MaesterK/atari-hypercard/pictures/flowmenu.png

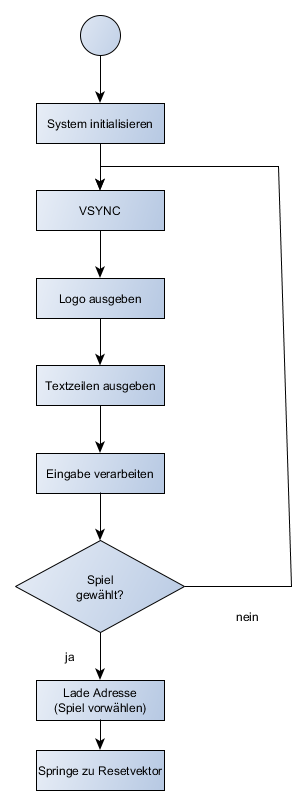
pictures/flowmenu.png
