MaesterK/atari-hypercard/pictures/galstate.png

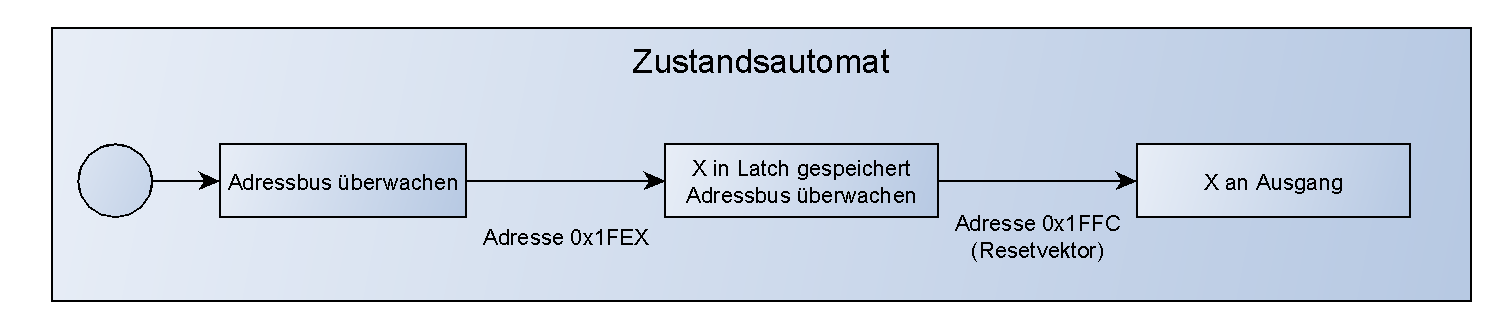
pictures/galstate.png
