MaesterK/atari-hypercard/pictures/menueexplained2.png

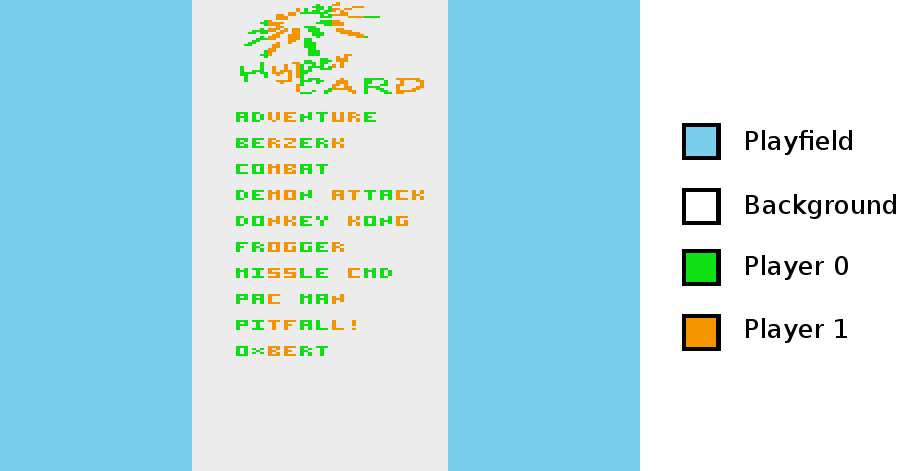
pictures/menueexplained2.png
