MaesterK/atari-hypercard/pictures/menueexplained_work.png

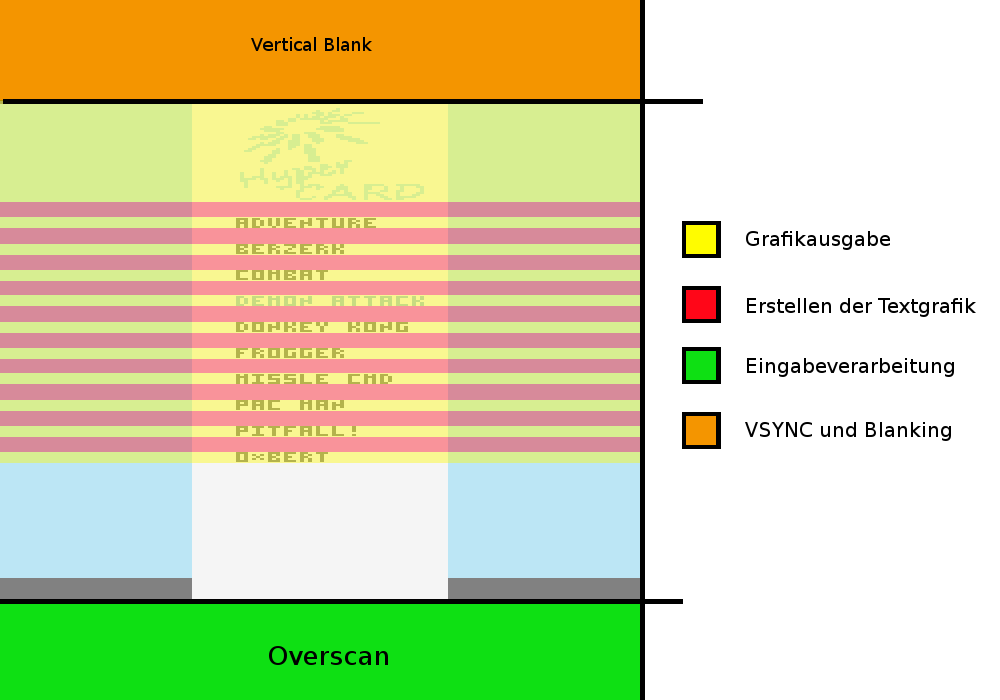
pictures/menueexplained_work.png
