MaesterK/atari-hypercard/pictures/supercard.png

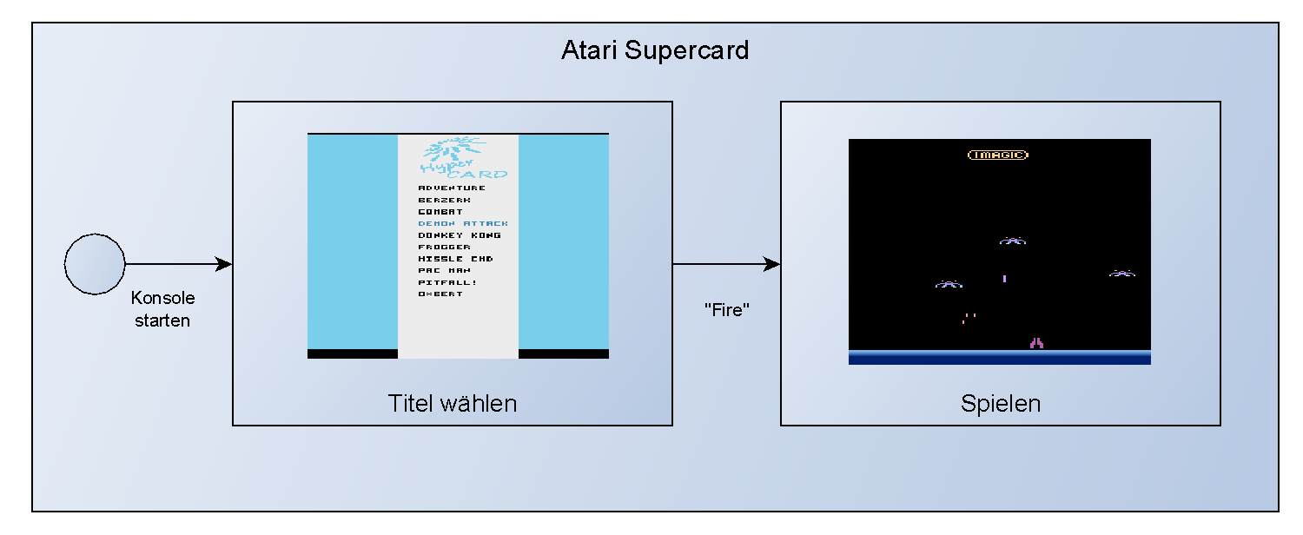
pictures/supercard.png
