MaesterK/atari-hypercard/pictures/wappen.PNG

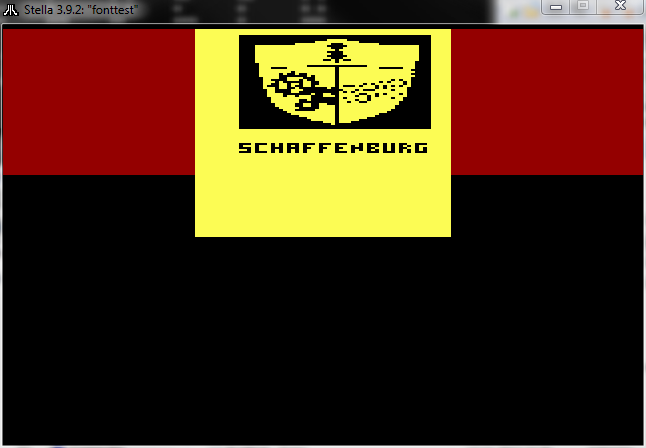
pictures/wappen.PNG
