MaesterK/atari-hypercard/pictures/debugger.PNG

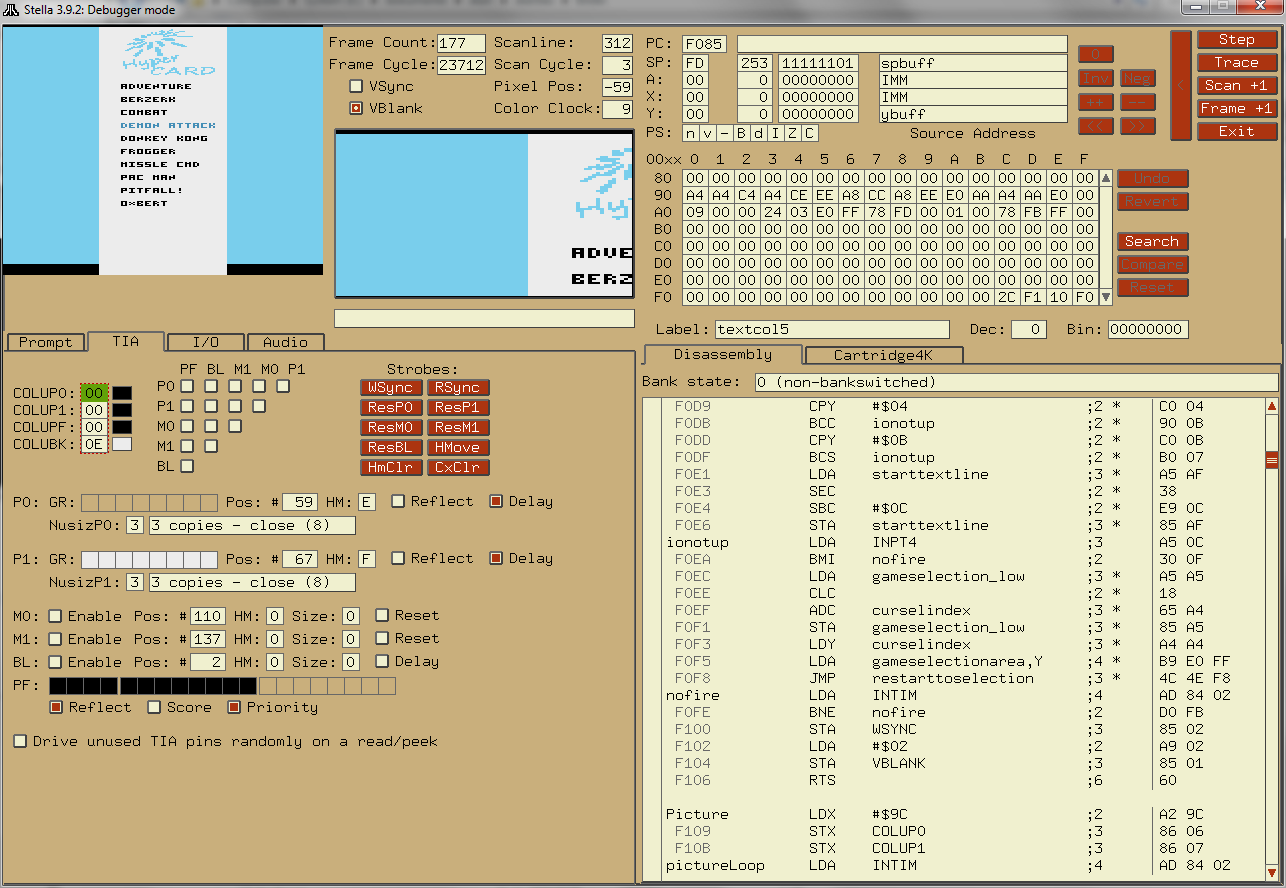
pictures/debugger.PNG
