MaesterK/atari-hypercard/tools/main2.cpp

#include <iostream>

/* run this program using the console pauser or add your own getch, system("pause") or input loop */


unsigned char pic[]={0x00,0x00,0x00,0x00,0x00,0x00
,0x00,0x00,0x00,0x40,0x00,0x00
,0x00,0x00,0x08,0xc0,0x00,0x00
,0x00,0x00,0x1d,0x07,0x00,0x00
,0x00,0x01,0x4d,0xd8,0x00,0x00
,0x00,0x01,0x5b,0xa0,0x00,0x00
,0x00,0x06,0xfe,0x30,0x00,0x00
,0x00,0x36,0x05,0xf0,0x00,0x00
,0x00,0x38,0x07,0x0f,0xf0,0x00
,0x00,0x38,0x00,0x00,0x00,0x00
,0x01,0x80,0x07,0xc0,0x00,0x00
,0x03,0xf0,0x0f,0xe0,0x00,0x00
,0x01,0xe0,0x03,0xe0,0x00,0x00
,0x00,0x30,0x70,0x00,0x00,0x00
,0x02,0xeb,0x38,0x60,0x00,0x00
,0x0f,0xdb,0x38,0x78,0x00,0x00
,0x1b,0x33,0x1c,0x3e,0x00,0x00
,0x00,0x67,0x1c,0x0f,0x00,0x00
,0x02,0xe7,0x08,0x03,0x80,0x00
,0x07,0xc7,0x60,0x00,0x00,0x00
,0x0c,0x06,0x60,0x00,0x00,0x00
,0x18,0x24,0x70,0x00,0x00,0x00
,0x30,0x60,0x70,0x00,0x00,0x00
,0x00,0x60,0x70,0x00,0x00,0x00
,0x00,0xc0,0x30,0x00,0x00,0x00
,0x01,0xc0,0x38,0x00,0x00,0x00
,0x01,0x80,0x38,0x00,0x00,0x00
,0x03,0x80,0x38,0x18,0x00,0x00
,0x01,0x00,0x00,0x50,0x00,0x00
,0x00,0x00,0x06,0x70,0x00,0x00
,0x00,0x00,0x67,0x70,0x00,0x00
,0x02,0x03,0x76,0x20,0x00,0x00
,0x02,0x09,0x94,0xa0,0x00,0x00
,0x42,0x49,0xbd,0xa0,0x00,0x00
,0x42,0x49,0xa7,0x00,0x00,0x00
,0x4e,0x5d,0xe0,0x00,0x00,0x00
,0x7b,0x75,0xc0,0x00,0x00,0x00
,0x61,0x25,0x80,0x00,0x00,0x00
,0x21,0x05,0x80,0x00,0x00,0x00
,0x20,0x04,0xb8,0x20,0xf8,0xfc
,0x20,0x3c,0xec,0x70,0xc4,0x46
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

};

//wappen
/*
{0xff,0xff,0xff,0xff,0xff,0xff
,0xff,0xff,0xff,0xff,0xff,0xff
,0xff,0xff,0xff,0xff,0xff,0xff
,0xff,0xff,0xfc,0x1f,0xff,0xff
,0xff,0xff,0xe0,0x03,0xff,0xff
,0xff,0xfc,0x01,0xc0,0x1f,0xff
,0xf0,0x00,0x03,0xe0,0x00,0x07
,0xf0,0x00,0x01,0xc0,0x00,0x07
,0xf0,0x00,0x00,0x80,0x00,0x07
,0xf0,0x00,0x03,0xc0,0x00,0x07
,0xf0,0x00,0x01,0xc0,0x00,0x07
,0xf0,0x00,0x03,0xe0,0x00,0x07
,0xf0,0x00,0x01,0xc0,0x00,0x07
,0xf0,0x00,0x06,0xb0,0x00,0x07
,0xf0,0x00,0x00,0x80,0x00,0x0f
,0xf8,0x00,0x00,0x00,0x00,0x0f
,0xf8,0x00,0x7f,0xff,0x00,0x0f
,0xf8,0xf0,0x00,0x80,0x1f,0x8f
,0xf8,0x00,0x00,0x80,0x00,0x1f
,0xf8,0x04,0x00,0x80,0x00,0x0f
,0xf8,0x2d,0x80,0x80,0x00,0x1f
,0xf8,0x3f,0xa0,0x80,0x00,0x0f
,0xfc,0x30,0xe0,0x80,0x00,0x1f
,0xfc,0xf1,0x60,0x80,0x02,0x9f
,0xfc,0x5f,0x30,0x80,0x14,0x5f
,0xfc,0xc9,0x30,0x81,0x40,0x5f
,0xfd,0xcb,0x20,0xba,0x2a,0x9f
,0xfc,0x4d,0xfd,0x80,0x28,0x3f
,0xfe,0x78,0xff,0xc5,0xc2,0x3f
,0xfe,0x79,0xff,0xa8,0x00,0x3f
,0xfe,0x1f,0xd9,0x83,0x28,0xbf
,0xfe,0x12,0x38,0x84,0xa0,0x3f
,0xff,0x00,0x3f,0xa0,0x82,0x7f
,0xff,0x01,0xbf,0x84,0x80,0x7f
,0xff,0x01,0xff,0x93,0x00,0xff
,0xff,0x83,0x33,0x80,0x00,0xff
,0xff,0x83,0x30,0x80,0x01,0xff
,0xff,0xc1,0xf0,0x80,0x01,0xff
,0xff,0xe3,0xe0,0x80,0x03,0xff
,0xff,0xf0,0x00,0x80,0x07,0xff
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
};
*/


int main(int argc, char** argv) {
	
	for (int i=0;i<sizeof(pic);i++){
//		printf("\tbyte $%x\n",pic[i]);
	}
	
	//spaltenweise gruppieren
	for(int i=0;i<6;i++){
		printf("col%i\n",i);
		for(int j=0;j<48;j++){
			printf("\tbyte $%x\n",pic[i+6*(48-j)]);
		}
	}
/*	testausgabe
	for(int i=0;i<48;i++){
		for(int j=0;j<6;j++){
			for(int k=0;k<8;k++){
			printf(((pic[i*6+j]>>(7-k))&1) ? "*" : " ");	
			}
			
		}
		printf("\n");
	}
*/	
	return 0;
}
